robotfishe/alkabot/3Dprint/tube support 0.8.stl

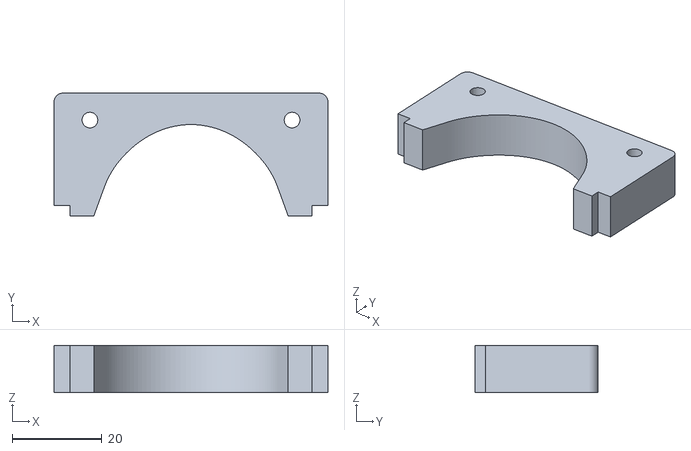
[picture p18: CAD file, 2021-07-23]
3Dprint/tube support 0.8.stl
61.0 x 27.3 x 10.5
