robotfishe/alkabot/3Dprint/bearing bottom.stl

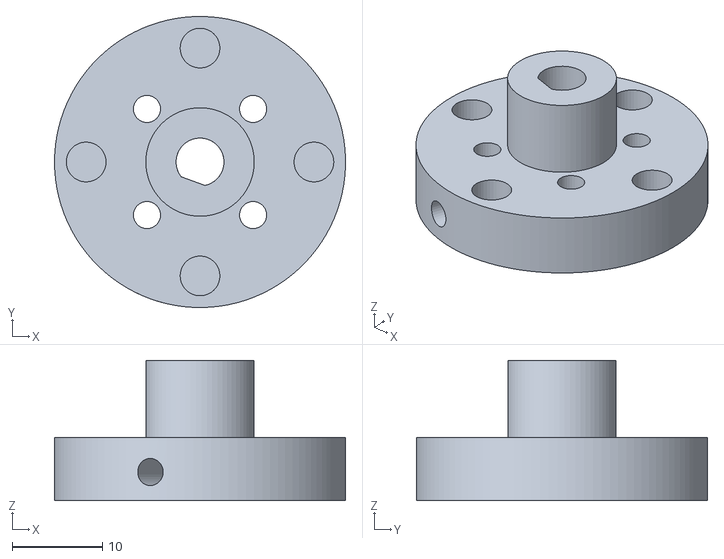
[picture p19: CAD file, 2021-07-23]
3Dprint/bearing bottom.stl
32.2 x 32.2 x 15.5
