robotfishe/alkabot/3Dprint/analog ph adapter.stl

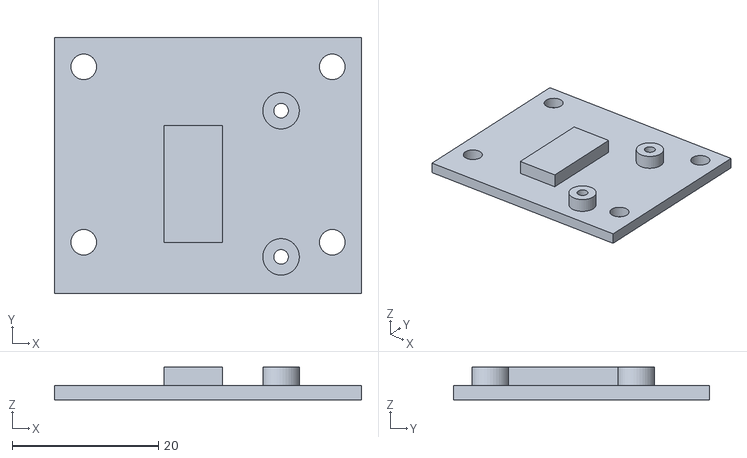
[picture p20: CAD file, 2021-07-23]
3Dprint/analog ph adapter.stl
42.0 x 35.0 x 4.50
