robotfishe/alkabot/3Dprint/reaction chamber lid.stl

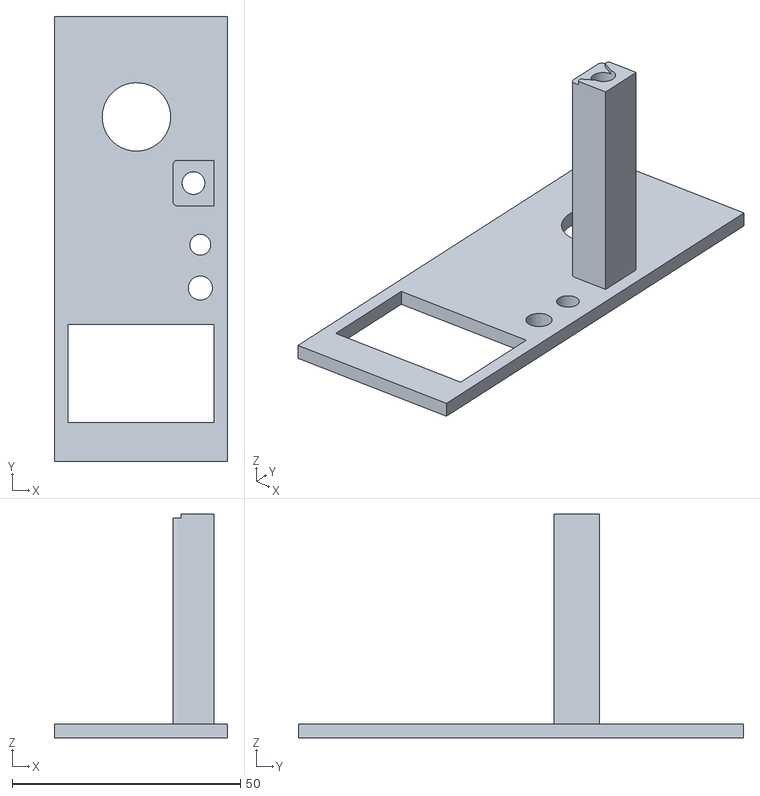
[picture p21: CAD file, 2021-07-23]
3Dprint/reaction chamber lid.stl
38.0 x 97.5 x 49.0
