robotfishe/alkabot/3Dprint/tube support 1.6.stl

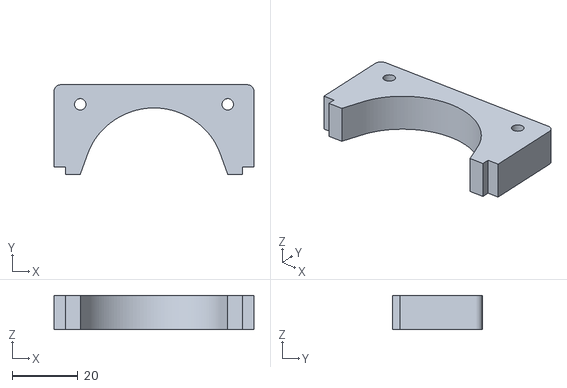
[picture p22: CAD file, 2021-07-23]
3Dprint/tube support 1.6.stl
61.0 x 27.3 x 10.5
