robotfishe/alkabot/3Dprint/magnet mount.stl

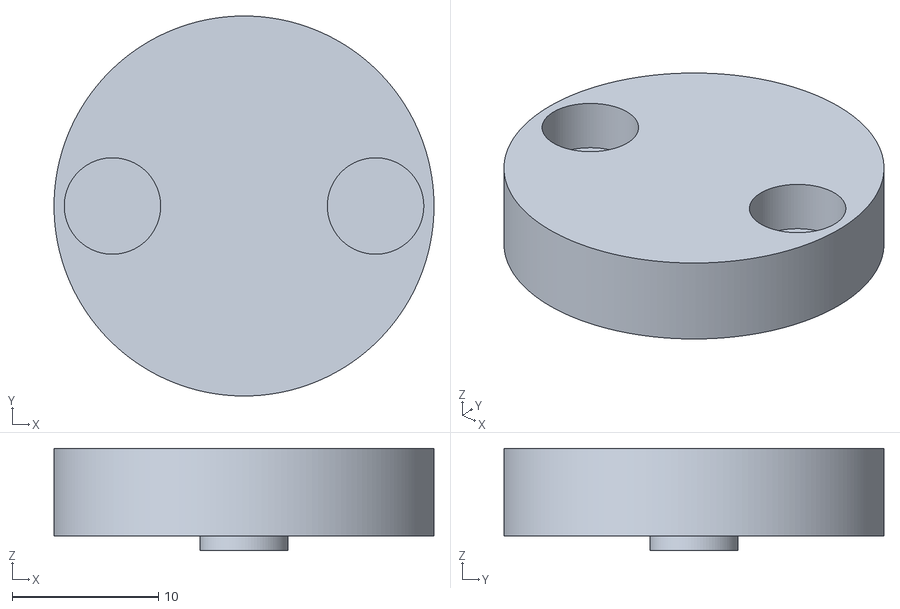
[picture p23: CAD file, 2021-01-12]
3Dprint/magnet mount.stl
26.0 x 26.0 x 7.00
